RBEGamer/WordClock/documentation/images/clock_wallmount_mounted.JPG

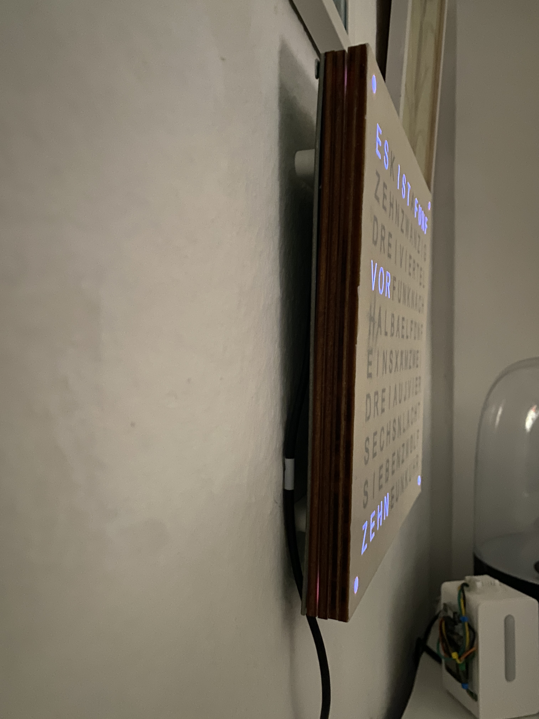
documentation/images/clock_wallmount_mounted.JPG
