RBEGamer/WordClock/documentation/images/colormode_coldwhite.JPG

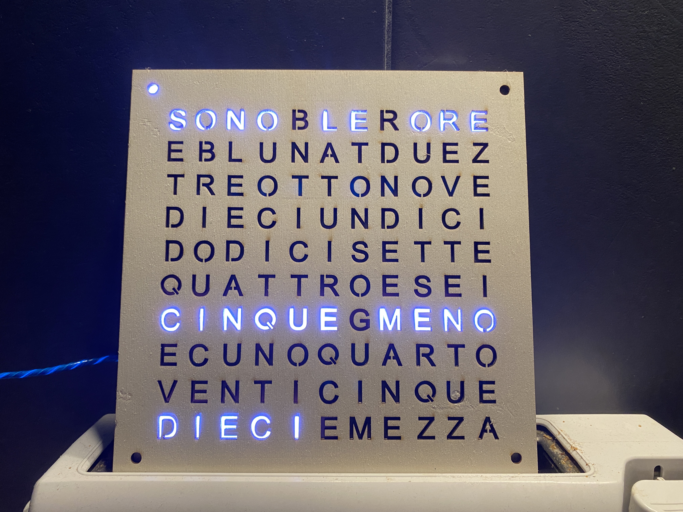
documentation/images/colormode_coldwhite.JPG
