RBEGamer/WordClock/documentation/images/colormode_rainbowseparate.JPG

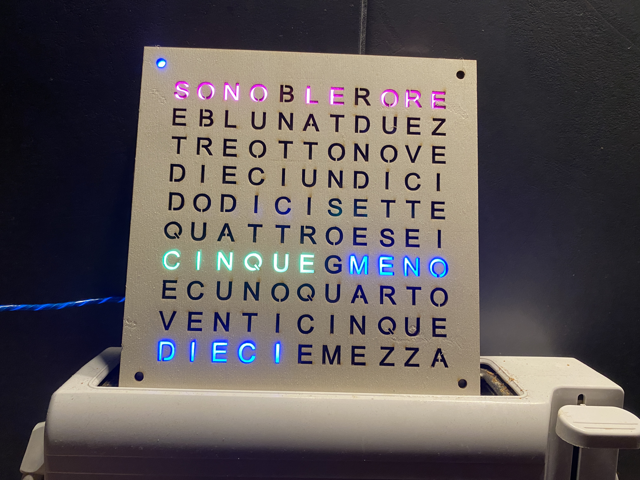
documentation/images/colormode_rainbowseparate.JPG
