RBEGamer/WordClock/documentation/images/IMG_0573.JPG

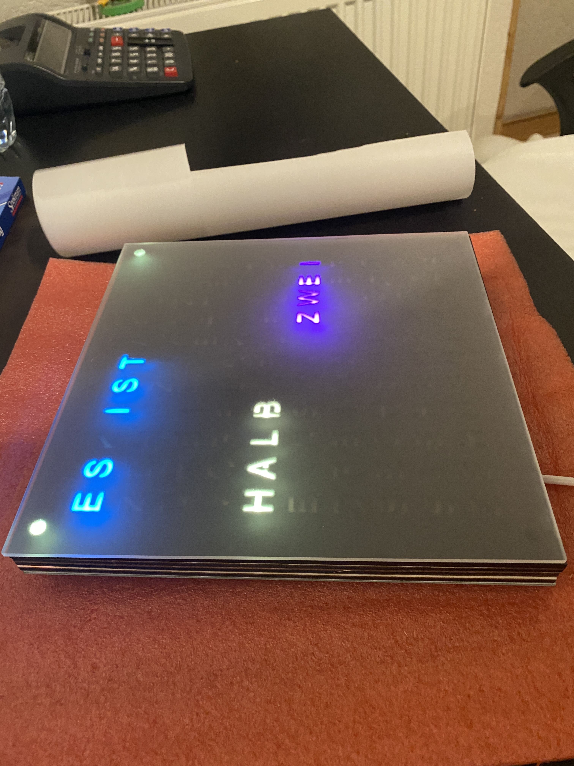
documentation/images/IMG_0573.JPG
