RBEGamer/WordClock/documentation/images/IMG_0575.JPG

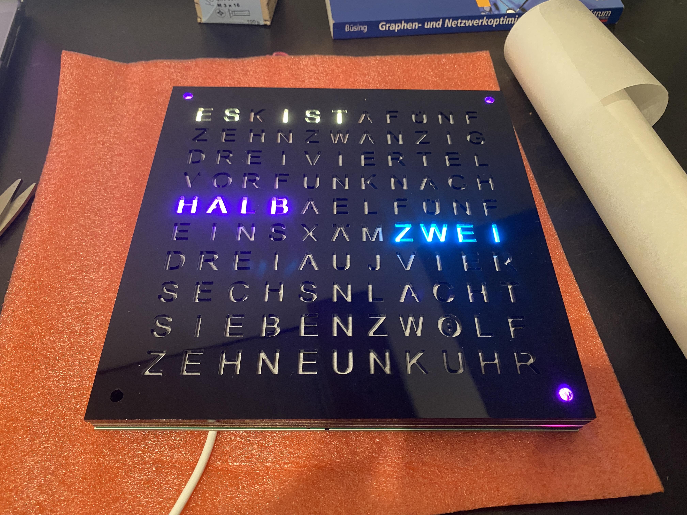
documentation/images/IMG_0575.JPG
