RBEGamer/WordClock/documentation/images/IMG_0579.JPG

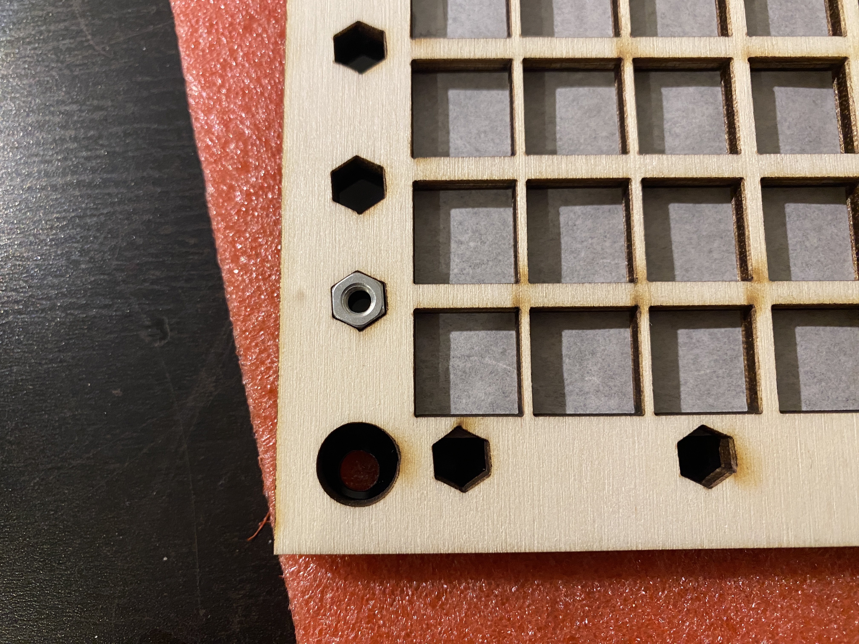
documentation/images/IMG_0579.JPG
