RBEGamer/WordClock/documentation/images/IMG_0956.JPG

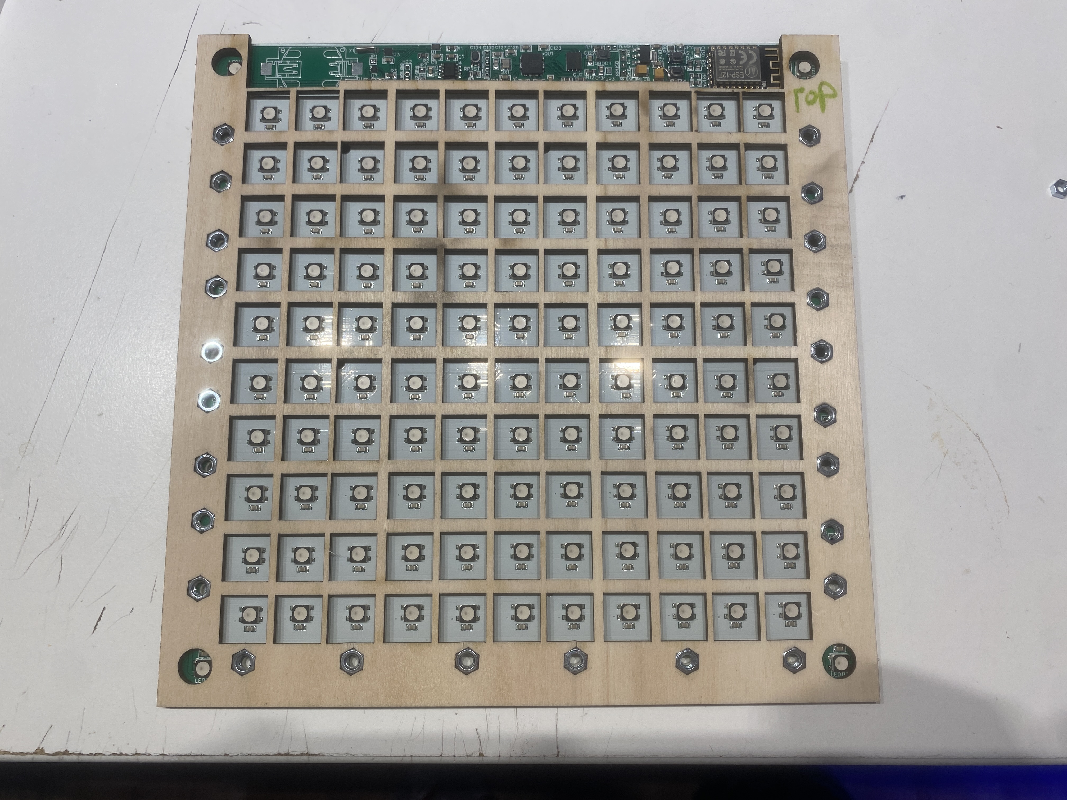
documentation/images/IMG_0956.JPG
