RBEGamer/WordClock/documentation/images/IMG_0957.JPG

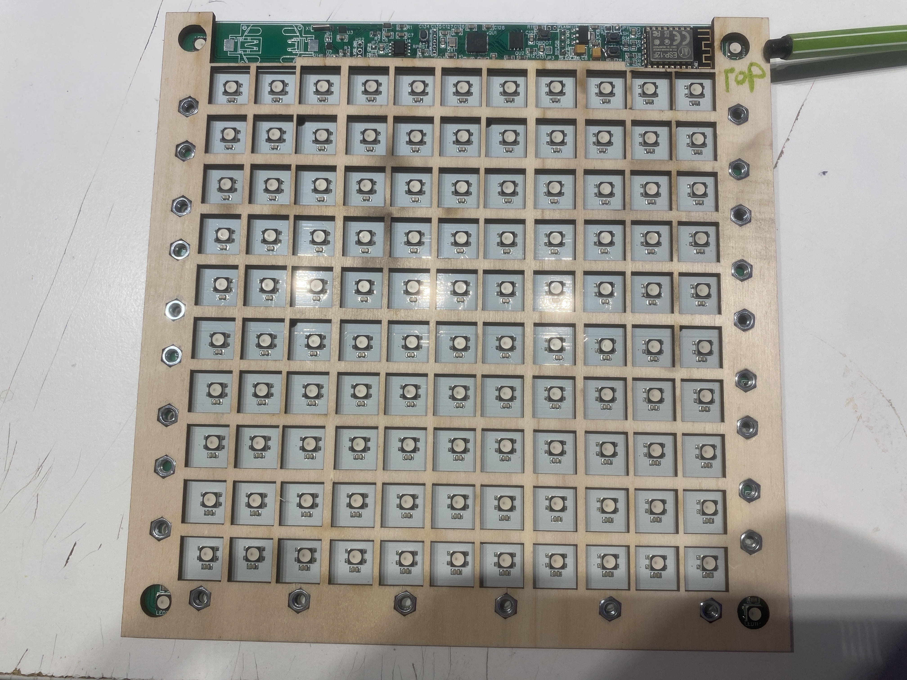
documentation/images/IMG_0957.JPG
