RBEGamer/WordClock/documentation/images/IMG_0964.JPG

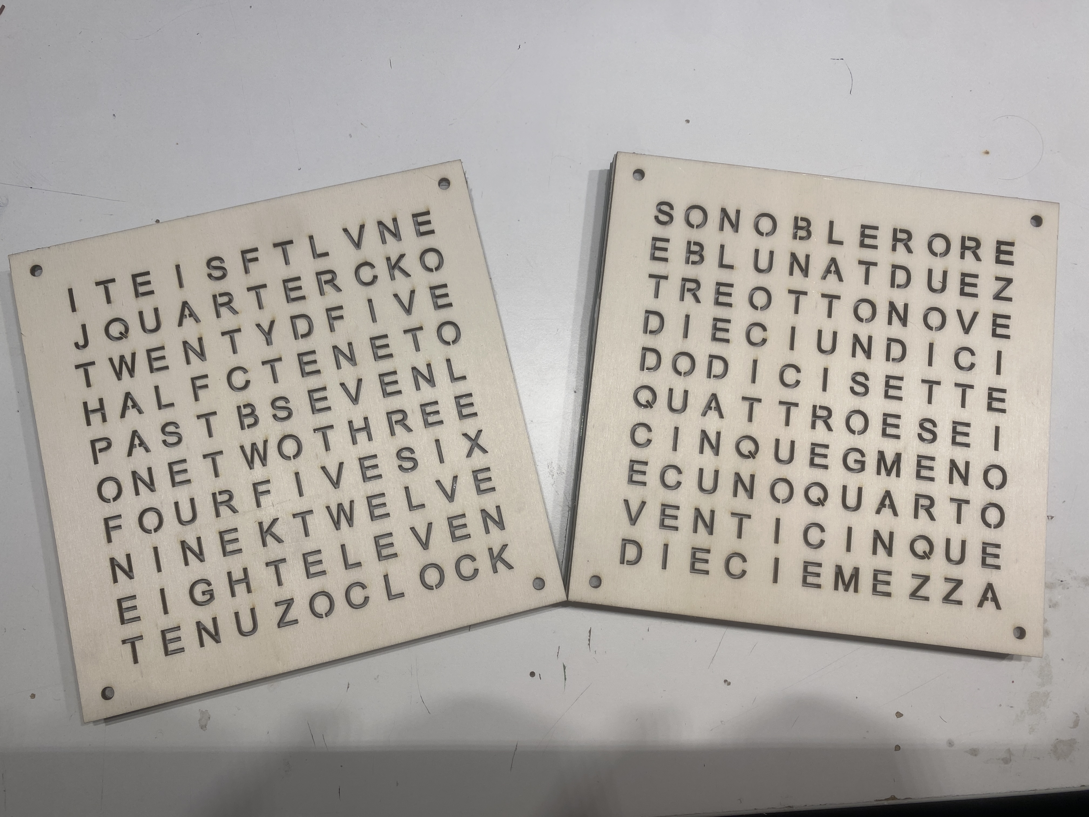
documentation/images/IMG_0964.JPG
