RBEGamer/WordClock/documentation/images/IMG_9901 2.jpg

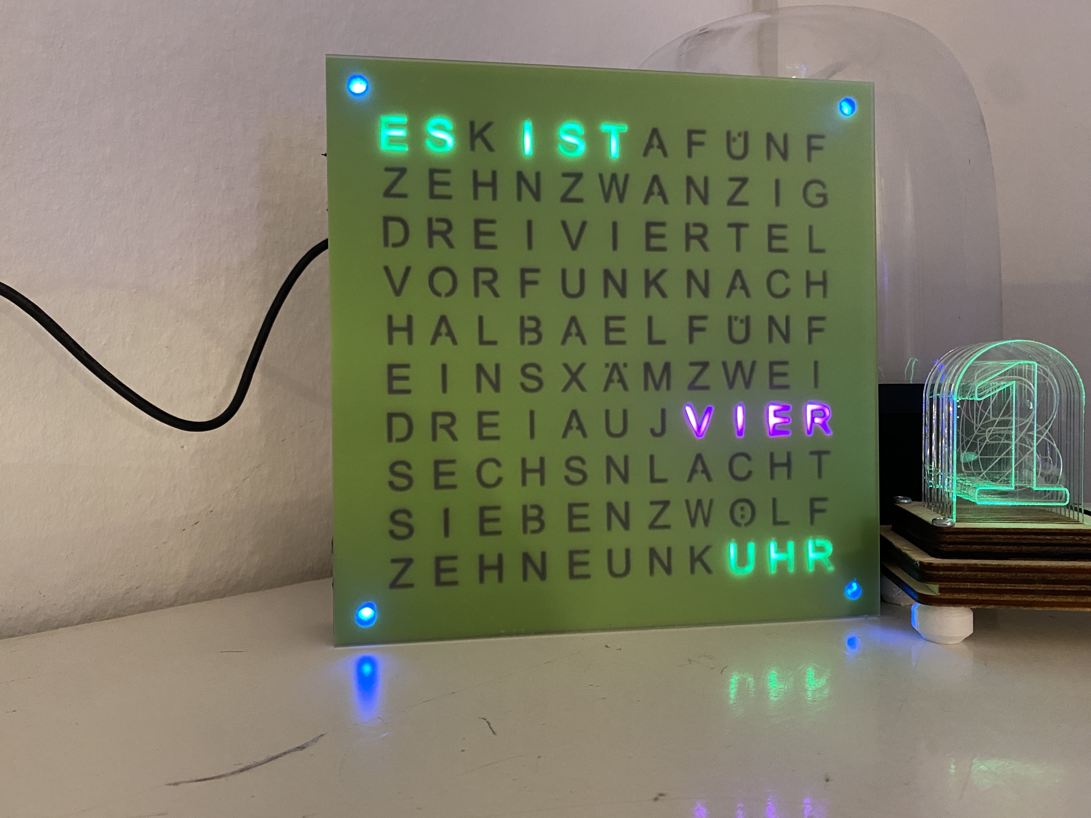
documentation/images/IMG_9901 2.jpg
