RBEGamer/WordClock/documentation/images/IMG_9902.jpg

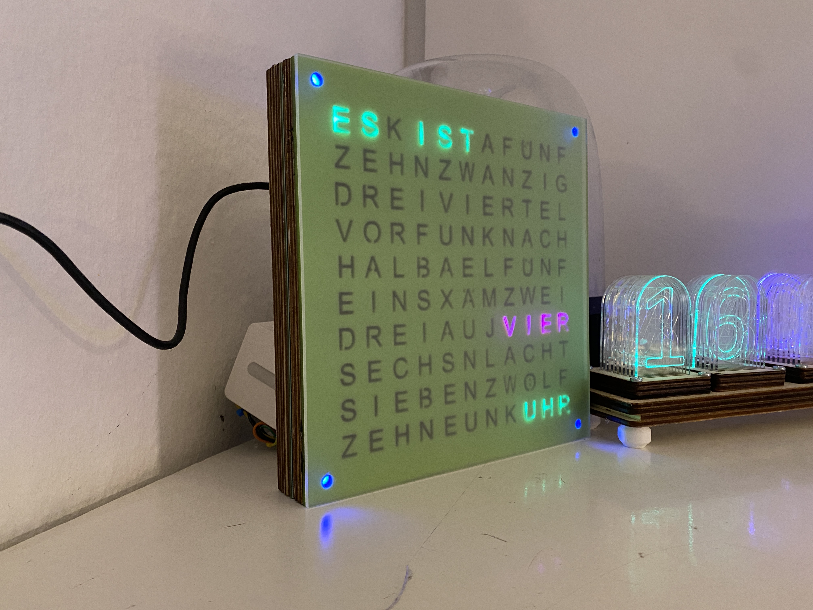
documentation/images/IMG_9902.jpg
