RBEGamer/WordClock/documentation/images/IMG_9903 2.jpg

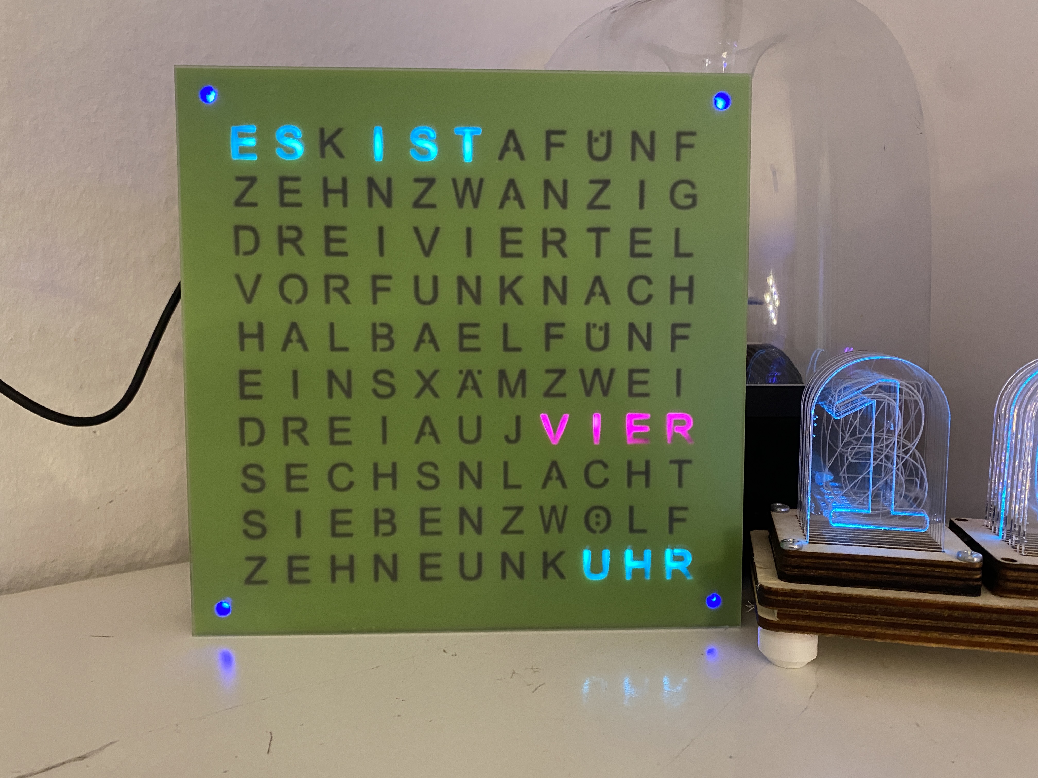
documentation/images/IMG_9903 2.jpg
