RBEGamer/WordClock/src/base/wordclock/src/wordclock_faceplate/wordclock_faceplate.hpp

#ifndef __WORDCLOCK_FACEPLATE_H__
#define __WORDCLOCK_FACEPLATE_H__
#include <pico/platform.h>
#include <PicoLed.hpp>
#include <vector>
#include <tuple>
#include "wordclock_faceplate_constants.h"
#include "../wifi_interface.hpp"

// THE TESTPATTERN FUNCTIONS DISPLAYS SOME SETTINGS LIKE VERSION, CONFIG
// SO MAKE SURE THE REQUIRED DEFINES ARE THERE
#ifndef VERSION
#define VERSION "1.0.0" // FORMAT "x.y.z"
#endif

#ifndef WORDCLOCK_PCBREV
#define WORDCLOCK_PCBREV 0
#endif

#ifndef RTCMODE
#if defined(USE_RP2040RTC)
#define RTCMODE 1
#elif defined(USE_I2CRTC_IF_PRESENT)
#define RTCMODE 2
#else
#define RTCMODE 0
#endif
#endif

#ifndef STORAGEMODE
#if defined(USE_FLASH_AS_EEPROM)
#define STORAGEMODE 1
#elif defined(USE_EEPROM_IF_PRESENT)
#define STORAGEMODE 2
#else
#define STORAGEMODE 0
#endif
#endif

#ifndef LIGHTMODE

#ifdef USE_BH1750_IF_PRESENT
#define LIGHTMODE 1
#else
#define LIGHTMODE 0
#endif
#endif

#define XOR(a, b) (a + b) % 2

class wordclock_faceplate
{
protected:
  enum class WORD_COLOR_CLASS
  {
    HOUR,
    MINUTE,
    COMMON,
    DEFAULT // DONT DELETE PLACE AS LAST ELEMENT used as length indicator
  };

  virtual void display_time_with_words(PicoLed::PicoLedController &_leds, const int _horig, const int _m, const int _s);
  void set_leds(PicoLed::PicoLedController &_leds, std::vector<std::tuple<int, int>> _word, const WORD_COLOR_CLASS _basecolor, const int _current_seconds);
  PicoLed::Color get_word_color_by_class(const WORD_COLOR_CLASS _basecolor, const int _current_seconds);
  int xy_to_led_index(const std::tuple<int, int> _xy);
  std::tuple<int, int> flip_xy(const std::tuple<int, int> _origin, const bool _flip);
  bool is_minutedot(const int _led_index);

public:
  enum class FACEPLATES
  {
    GERMAN,
    ENGLISH,
    ITALIAN,
    BELGIAN,
    BINARY,
    DOTS,
    TEST // DONT DELETE TEST PLACE AS lAST ELEMENT used as length indicator
  };


  static inline const int FACEPLATE_LENGHT = ((int)FACEPLATES::TEST);

  static inline const std::string FACEPLATE_NAMES[FACEPLATE_LENGHT] = {
      "GERMAN",
      "ENGLISH",
      "ITALIAN",
      "BELGIAN",
      "BINARY",
      "DOTS"
    };



  enum class COLORMODE
  {
    RAINBOW_SEPARATE = 0,
    RAINBOW_SAME = 1,
    COLD_WHITE = 2,
    WARM_WHITE = 3,
    LENGTH // DONT DELETE or USE
  };

  struct FACEPLATE_CONFIG
  {
    bool flip_state;
    FACEPLATES current_faceplate;
    COLORMODE color_mode;
    uint8_t dotbrightness;
    bool blinkendots;
    FACEPLATE_CONFIG()
    {
      flip_state = false;
      current_faceplate = FACEPLATES::GERMAN;
      color_mode = COLORMODE::COLD_WHITE;
      dotbrightness = WORDCLOCK_DOTBRIGHTNESS;
      blinkendots = (bool)WORDCLOCK_BLINKENDOTS;
    }
  };
  // INLINE IN C++17 no init in cpp needed
  inline static struct FACEPLATE_CONFIG config;

  wordclock_faceplate();
  virtual ~wordclock_faceplate();

  void display_testpattern(PicoLed::PicoLedController &_leds);
  void display_time(PicoLed::PicoLedController &_leds, const int _h, const int _m, const int _s);
  void set_colormode(COLORMODE _colormode);
};

#endif
