RBEGamer/WordClock/src/base/wordclock/src/wordclock_faceplate/wordclock_faceplate_include.h

#include "wordclock_faceplate.hpp"
#include "wordclock_faceplate_german.hpp"
#include "wordclock_faceplate_italian.hpp"
#include "wordclock_faceplate_english.hpp"
#include "wordclock_faceplate_binary.hpp"
#include "wordclock_faceplate_dots.hpp"
