RBEGamer/WordClock/src/base/wordclock/src/rtc/rtc_i2c.hpp

#ifndef __RTC_I2C_HPP__
#define __RTC_I2C_HPP__

#include "pico/stdlib.h"
#include "pico/util/datetime.h"
#include "hardware/rtc.h"

#include "../helper.h"
#include "rtc.hpp"

class rtc_i2c: public rtc
{

private:
    uint8_t bcdToDec(const uint8_t _value);
    uint8_t decToBcd(const uint8_t _value);
    datetime_t read_rtc_raw();
public:

    rtc_i2c();
    ~rtc_i2c();

    void set_rtc_time(const std::string _time, bool _initial) override;
    void set_rtc_time(const signed char _h, const signed char _m, const signed char _s, bool _initial) override;
    void set_rtc_date(const std::string _time) override;
    void set_rtc_date(const signed char _day, const signed char _month, const int _year) override;
    void init() override;
    datetime_t read_rtc() override;
    void set_initial_time() override;


};
#endif
