RBEGamer/WordClock/src/base/wordclock/src/rtc/rtc_ds1307.h

#ifndef __RTC_DS1307_H__
#define __RTC_DS1307_H__

#include "pico/stdlib.h"
#include "pico/util/datetime.h"
#include "hardware/rtc.h"

#include "../helper.h"
#include "rtc.h"

class rtc_ds1307: public rtc
{

private:
    //const int rtc_i2c_addr = RTC_I2C_ADDR;
    uint8_t bcdToDec(const uint8_t _value);
    uint8_t decToBcd(const uint8_t _value);

public:

    rtc_ds1307();
    ~rtc_ds1307();

    void set_rtc_time(const std::string _time) override;
    void set_rtc_time(const uint8_t _h, const uint8_t _m, const uint8_t _s) override;
    void init_rtc() override;
    datetime_t read_rtc() override;


};
#endif
