RBEGamer/WordClock/documentation/images/IMG_0570.JPG

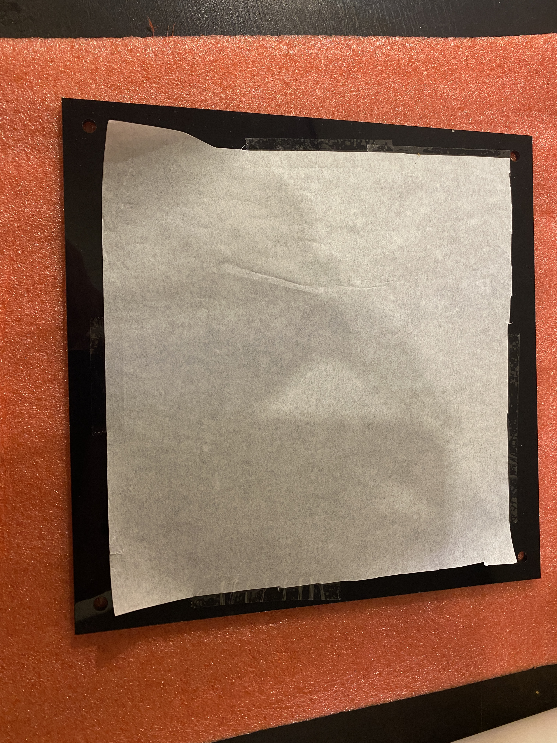
documentation/images/IMG_0570.JPG
