RBEGamer/WordClock/documentation/images/IMG_9875.jpg

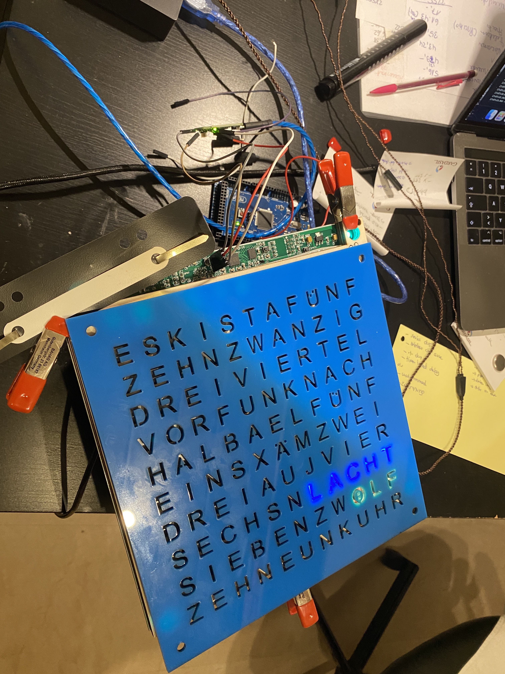
documentation/images/IMG_9875.jpg
