RBEGamer/WordClock/documentation/images/IMG_9897 2.jpg

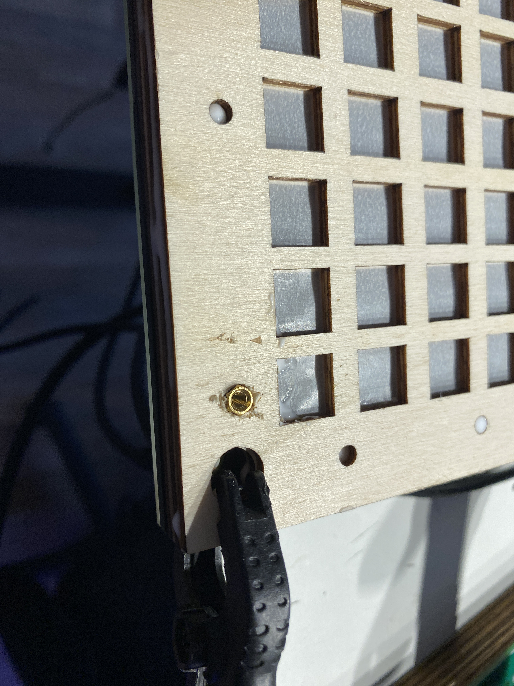
documentation/images/IMG_9897 2.jpg
